TheScientist101/buildpad/firmware/kmk/kmk/quickpin/pro_micro/elite_pi.py

import board

pinout = [
    board.D0,
    board.D1,
    None,  # GND
    None,  # GND
    board.D2,
    board.D3,
    board.D4,
    board.D5,
    board.D6,
    board.D7,
    board.D8,
    board.D9,
    board.D21,
    board.D23,
    board.D20,
    board.D22,
    board.D26,
    board.D27,
    board.D28,
    board.D29,
    None,  # VCC
    None,  # RUN
    None,  # GND
    None,  # RAW
]
