TheScientist101/buildpad/firmware/kmk/kmk/utils.py

try:
    from typing import Optional
except ImportError:
    pass

from supervisor import ticks_ms

from usb_cdc import console


def clamp(x: int, bottom: int = 0, top: int = 100) -> int:
    return min(max(bottom, x), top)


_debug_enabled = None


class Debug:
    '''default usage:
    debug = Debug(__name__)
    '''

    def __init__(self, name: str = __name__):
        self.name = name

    def __call__(self, *message: str, name: Optional[str] = None) -> None:
        if not name:
            name = self.name
        print(ticks_ms(), end=' ')
        print(name, end=': ')
        print(*message, sep='')

    @property
    def enabled(self) -> bool:
        global _debug_enabled
        if (
            _debug_enabled is None
            and console
            and console.connected
            and console.out_waiting == 0
        ):
            return True
        return bool(_debug_enabled)

    @enabled.setter
    def enabled(self, enabled: bool):
        global _debug_enabled
        _debug_enabled = enabled
